ZackFreedman/Singularitron/Enclosure/STL's/Keycap 4.stl

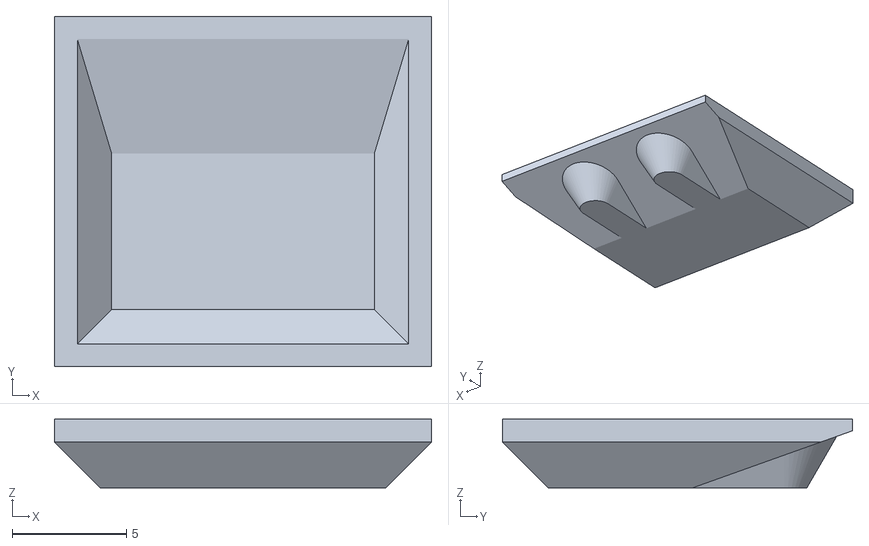
[picture p21: CAD file, 2020-01-06]
Enclosure/STL's/Keycap 4.stl
16.5 x 15.3 x 3.00
