ZackFreedman/Singularitron/SingularitronFirmware/states.h

#define sleeping 0
#define homeScreen 1
#define cartApp 2
#define cartQuickfire 3
#define cartInsertInterstitial 4
#define cartEjectInterstitial 5

#define systemMenu 20
#define systemApp 21

#define defenseArming 30
#define defenseMode 31

#define indeterminateState 255
